TehoorMarjan/Ignis/hardware/IgnisV2/out/IgnisV2.png

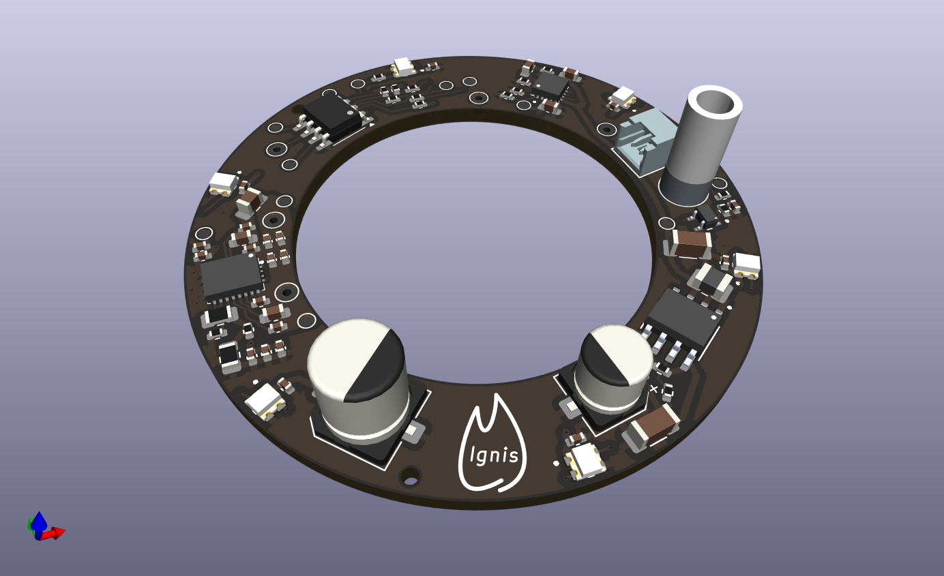
hardware/IgnisV2/out/IgnisV2.png
