TehoorMarjan/Ignis/mechanical/cad/TestStandV2/TestStandV2-Guide.stl

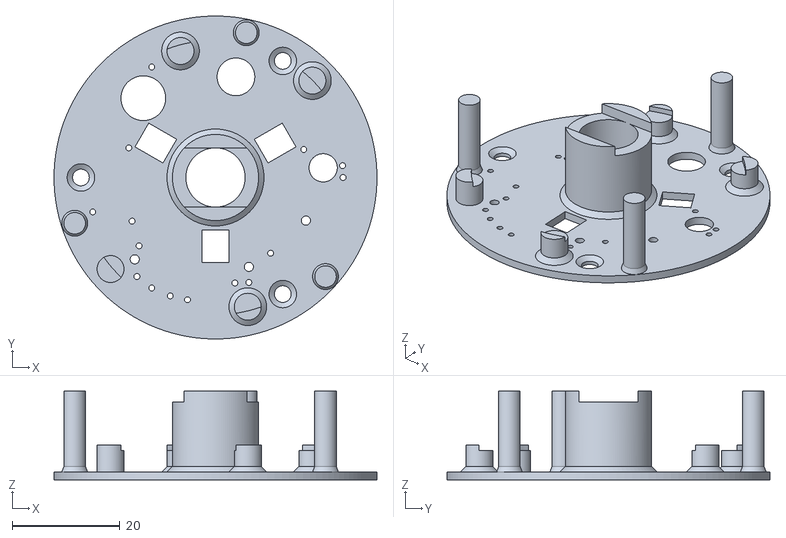
[picture p38: CAD file, 2025-09-15]
mechanical/cad/TestStandV2/TestStandV2-Guide.stl
60.0 x 60.0 x 16.5
