TehoorMarjan/Ignis/mechanical/cad/SW18030/SW18030.FCStd

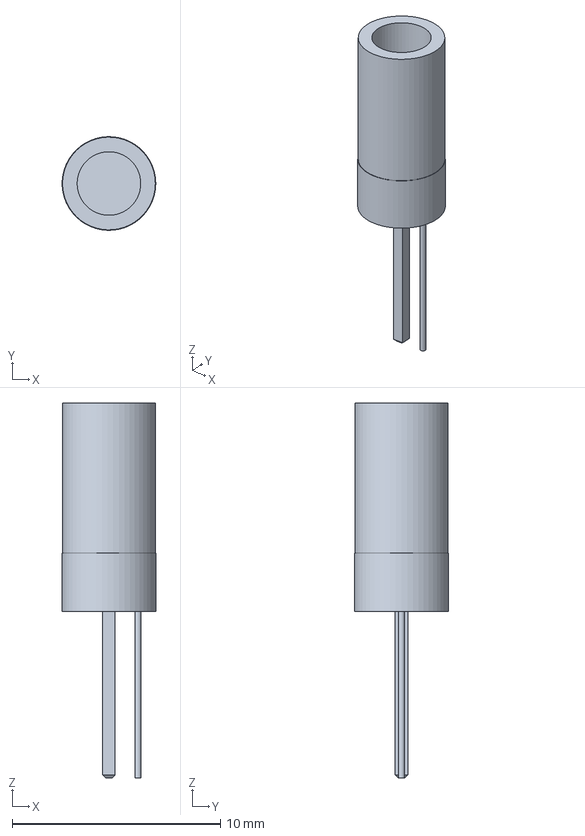
[picture p39: CAD file, 2025-08-25]
mechanical/cad/SW18030/SW18030.FCStd
4.50 x 4.50 x 18.0 mm
