TehoorMarjan/Ignis/mechanical/cad/TestStand/TestStand-Hook.stl

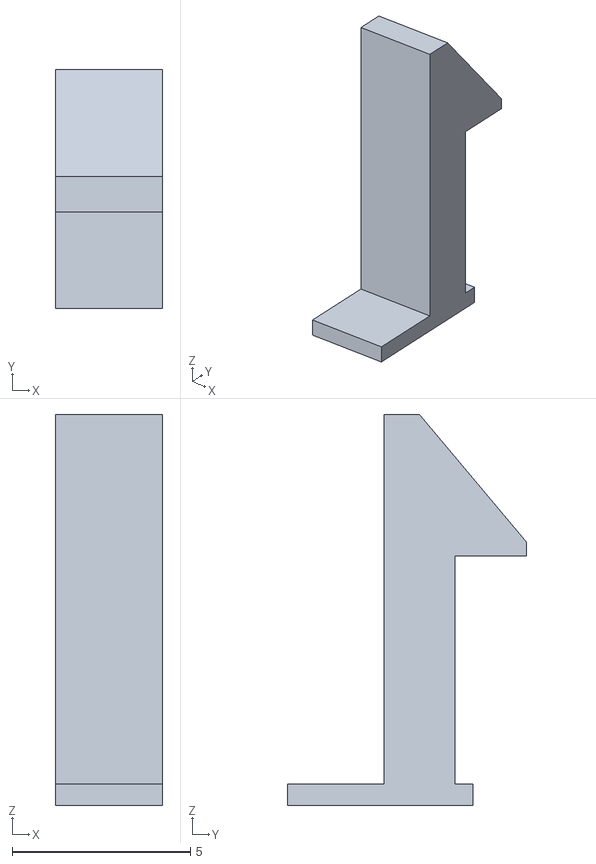
[picture p40: CAD file, 2025-09-08, an earlier design]
mechanical/cad/TestStand/TestStand-Hook.stl
3.00 x 6.70 x 11.0
