TehoorMarjan/Ignis/mechanical/cad/TestStand/TestStand-Top.stl

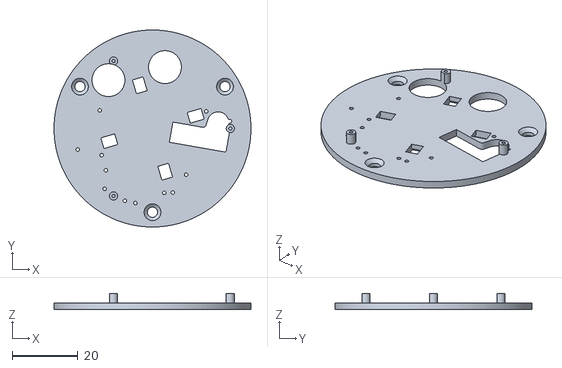
[picture p41: CAD file, 2025-09-08, an earlier design]
mechanical/cad/TestStand/TestStand-Top.stl
60.0 x 60.0 x 5.00
